bunedoggle/river-monster/Simple_xmit_example/ask_receiver/ask_receiver.ino

// ask_receiver.pde
// -*- mode: C++ -*-
// Simple example of how to use RadioHead to receive messages
// with a simple ASK transmitter in a very simple way.
// Implements a simplex (one-way) receiver with an Rx-B1 module

#include <RH_ASK.h>
#include <SPI.h> // Not actualy used but needed to compile

//RH_ASK::RH_ASK(uint16_t speed, uint8_t rxPin, uint8_t txPin, uint8_t pttPin, bool pttInverted)
RH_ASK driver( 1200, A1, 3, 4, 5 );
//RH_ASK driver;

void setup()
{
  // Power pin
  pinMode(A0,OUTPUT);
  digitalWrite(A0, HIGH);
  
  // Gnd pin
  pinMode(A3, LOW);
  digitalWrite(A3, LOW);
  
  Serial.begin(9600);	// Debugging only
  if (!driver.init())
       Serial.println("init failed");
}

void loop()
{
    uint8_t buf[RH_ASK_MAX_MESSAGE_LEN];
    uint8_t buflen = sizeof(buf);

    if (driver.recv(buf, &buflen)) // Non-blocking
    {
	int i;

	// Message with a good checksum received, dump it.
	driver.printBuffer("Got:", buf, buflen);
    }
}
